Suya1671/woagboard/pictures/journal/jul-6-v18.png

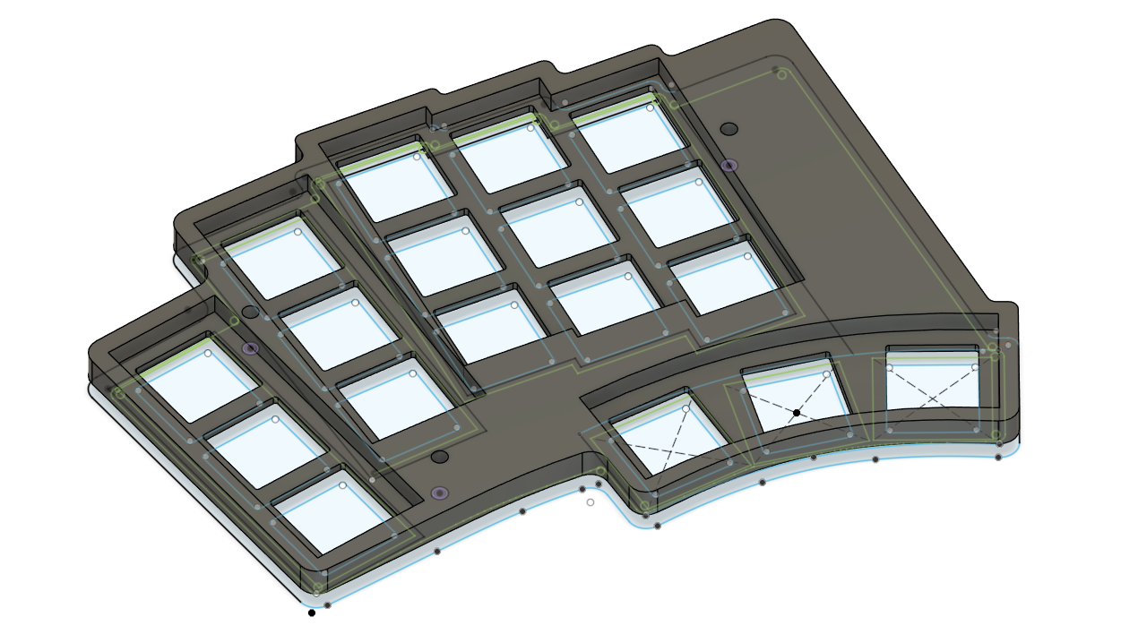
pictures/journal/jul-6-v18.png
