Suya1671/woagboard/pictures/journal/jul-6-v19.png

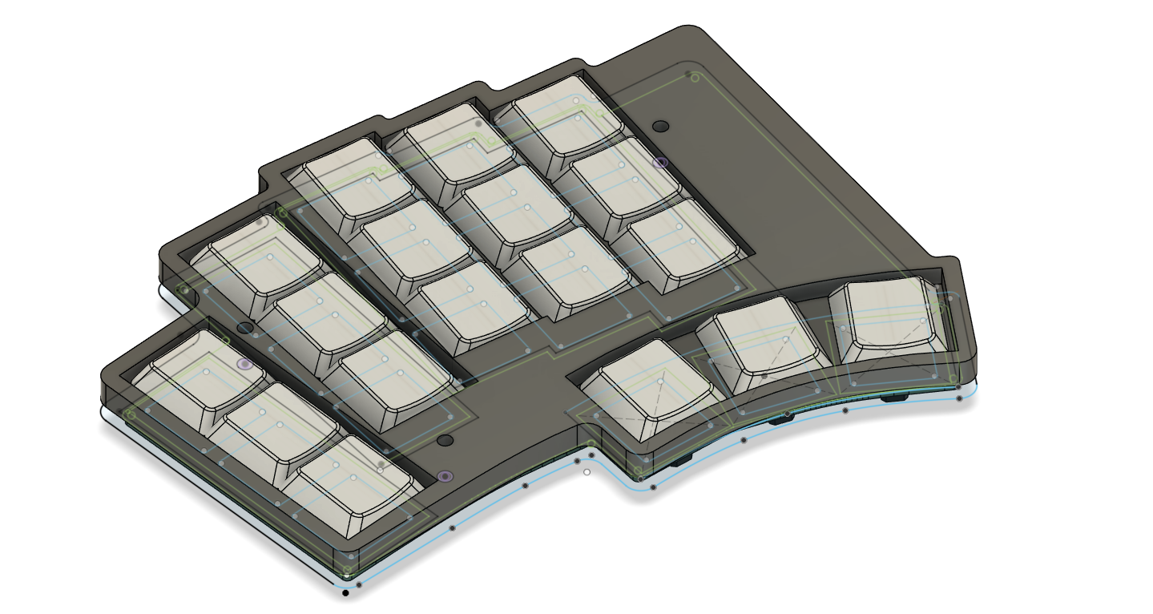
pictures/journal/jul-6-v19.png
